aokiam/bio-motion-light-system/hardware/schematics/biomotion-light-system/smart cosplay.kicad_sch

## KiCad design hardware/schematics/biomotion-light-system/smart cosplay.kicad_sch (2026-09-25, an earlier design)

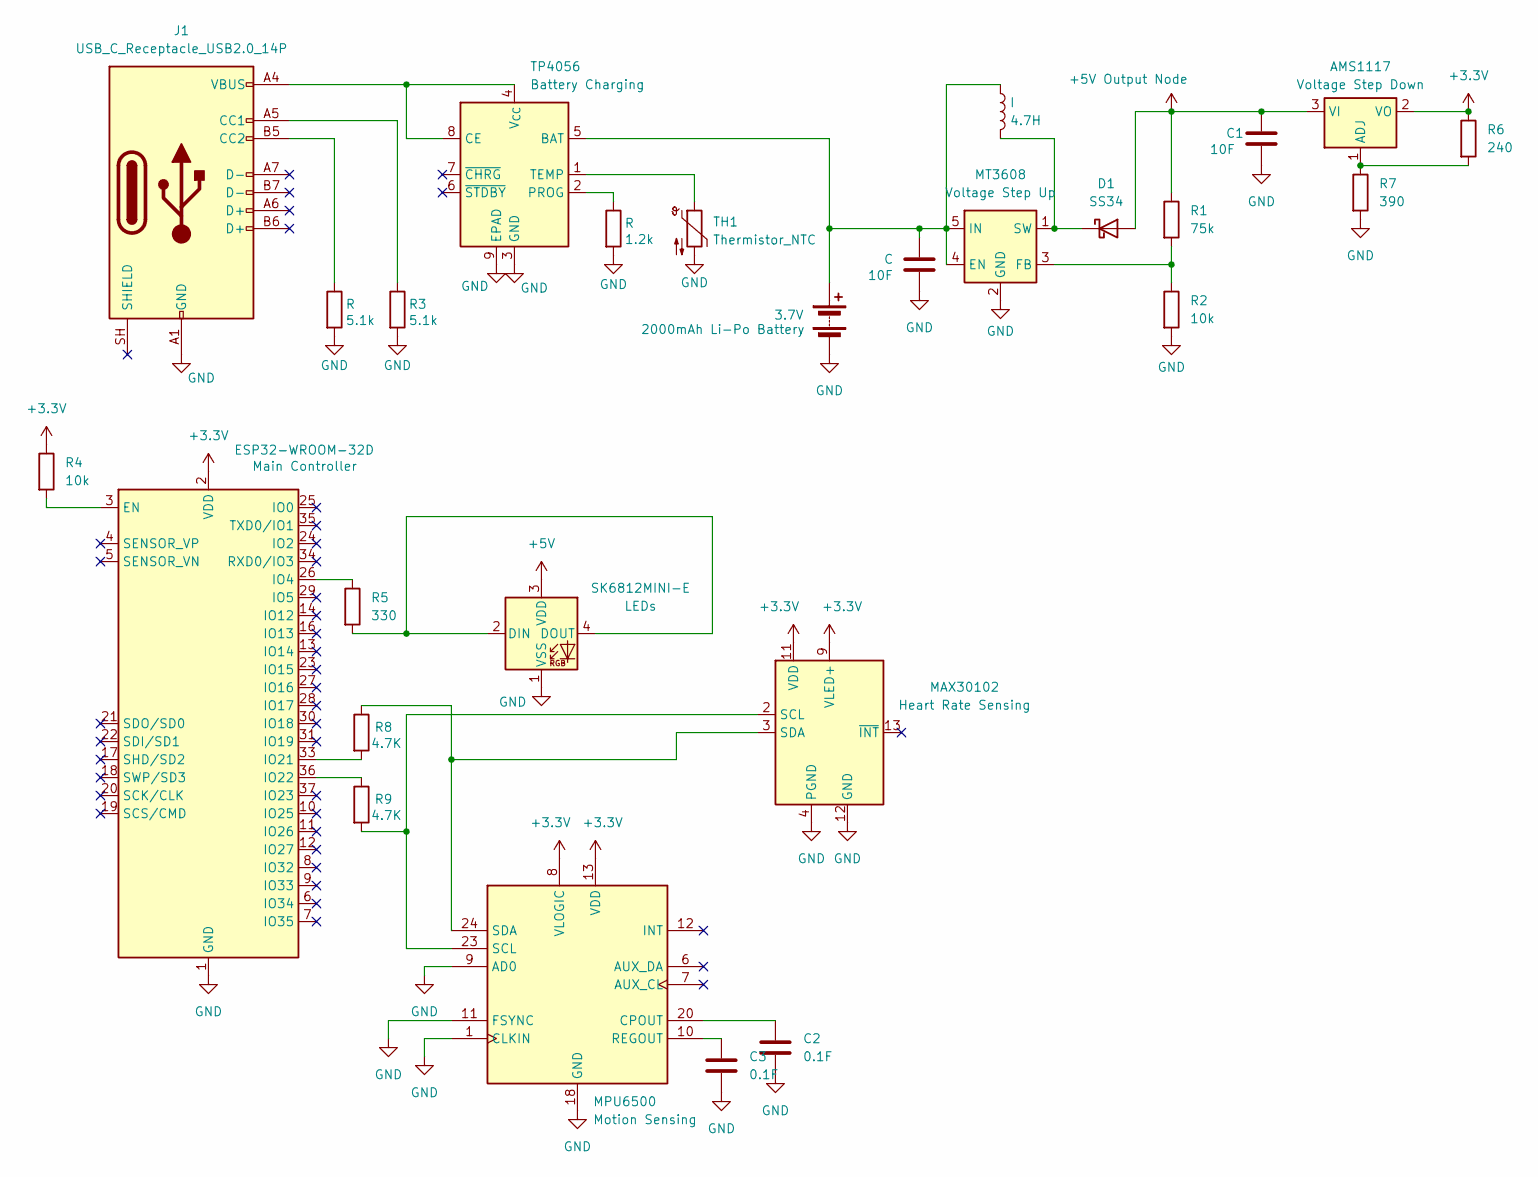
[picture p5: schematic smart cosplay.kicad_sch]

Parts:
3.7V: 2000mAh Li-Po Battery
AMS1117: Voltage Step Down; SOT-223-3_TabPin2
C, C1: 10F
C2, C3: 0.1F
D1: SS34; D_SMA
ESP32-WROOM-32D: Main Controller; ESP32-WROOM-32D
I: 4.7H
J1: USB_C_Receptacle_USB2.0_14P
MAX30102: Heart Rate Sensing; Maxim_OLGA-14_3.3x5.6mm_P0.8mm
MPU6500: Motion Sensing; InvenSense_QFN-24_4x4mm_P0.5mm
MT3608: Voltage Step Up; SOT-23-6
R, R3: 5.1k
R1: 75k
R2, R4: 10k
R5: 330
R6: 240
R7: 390
R8, R9: 4.7K
SK6812MINI-E: LEDs; LED_SK6812MINI-E_3.2x2.8mm_P1.5mm_ReverseMount
TH1: Thermistor_NTC
TP4056: Battery Charging; SOIC-8-1EP_3.9x4.9mm_P1.27mm_EP2.41x3.3mm_ThermalVias

Connections:
+3.3V: AMS1117.2 (VO), ESP32-WROOM-32D.2 (VDD), MAX30102.9 (VLED+), MAX30102.10 (VLED+), MAX30102.11 (VDD), MPU6500.8 (VLOGIC), MPU6500.13 (VDD), R4.1, R6.1
+5V: SK6812MINI-E.3 (VDD)
+5V Output Node: AMS1117.3 (VI), C1.1, D1.2 (A), R1.1
GND: 3.7V.2 (-), C.2, C1.2, C2.2, C3.2, ESP32-WROOM-32D.1 (GND), ESP32-WROOM-32D.15 (GND), ESP32-WROOM-32D.38 (GND), ESP32-WROOM-32D.39 (GND), J1.A1 (GND), J1.A12 (GND), J1.B1 (GND), J1.B12 (GND), MAX30102.4 (PGND), MAX30102.12 (GND), MPU6500.1 (CLKIN), MPU6500.9 (AD0), MPU6500.11 (FSYNC), MPU6500.18 (GND), MT3608.2 (GND), R.2, R2.2, R3.2, R7.2, SK6812MINI-E.1 (VSS), TH1.2, TP4056.3 (GND), TP4056.9 (EPAD)
unnamed: 3.7V.1 (+), C.1, I.1, MT3608.4 (EN), MT3608.5 (IN), TP4056.5 (BAT)
unnamed: AMS1117.1 (ADJ), R6.2, R7.1
unnamed: C2.1, MPU6500.20 (CPOUT)
unnamed: C3.1, MPU6500.10 (REGOUT)
unnamed: D1.1 (K), I.2, MT3608.1 (SW)
unnamed: ESP32-WROOM-32D.3 (EN), R4.2
unnamed: ESP32-WROOM-32D.26 (IO4), R5.1
unnamed: ESP32-WROOM-32D.33 (IO21), R8.2
unnamed: ESP32-WROOM-32D.36 (IO22), R9.1
unnamed: J1.A4 (VBUS), J1.A9 (VBUS), J1.B4 (VBUS), J1.B9 (VBUS), TP4056.4 (V_{CC}), TP4056.8 (CE)
unnamed: J1.A5 (CC1), R3.1
unnamed: J1.B5 (CC2), R.1
unnamed: MAX30102.2 (SCL), MPU6500.23 (SCL), R9.2
unnamed: MAX30102.3 (SDA), MPU6500.24 (SDA), R8.1
unnamed: MT3608.3 (FB), R1.2, R2.1
unnamed: R5.2, SK6812MINI-E.2 (DIN), SK6812MINI-E.4 (DOUT)
unnamed: R.1, TP4056.2 (PROG)
unnamed: TH1.1, TP4056.1 (TEMP)
